DC801/DC25PartyBadge/Software/lcd.c

/*
 * @file lcd.c
 *
 * @date May 24, 2017
 * @author hamster
 *
 * @brief Routines to draw to the screen specific to the dc801 badge - we mostly use the build in gfx calls
 *
 */

#include "system.h"
#include "lcd.h"
